jsain78480/TpSystemeMicroControleur/firmware/firmwarev1/Core/Inc/led.h

/*
 * led.h
 *
 *  Created on: Mar 7, 2024
 *      Author: julisain95
 */


#ifndef INC_LED_H_
#define INC_LED_H_

#include "main.h"

// Structure pour la gestion la led Status :
typedef struct {
	uint8_t luminosite ;
	uint8_t updown;
} Led_t;

// Fonction qui démarre le timer
void LedStart(void);

// Fonction qui configure le rapport cyclique de la PWM
void LedSetValue(uint8_t val);

// fonction qui incrémente puis décremente la luminosité de la led
void LedPulse(void);

#endif
